sonofusion82/ds32khz_clock/time_update.c

/* 
 * File:   time_update.c
 * Author: YewMing, Chen (fusion82@gmail.com)
 *
 * Created on November 15, 2015, 12:07 AM
 */

#include "time_update.h"

extern volatile unsigned char tmr1_ticked;
extern unsigned char display_ticked;
extern unsigned char low_power_enable;
unsigned char hours = 0;
unsigned char minutes = 0;
unsigned char seconds = 0;
unsigned int temp = 0;

/* unsigned char to 2 byte BCD
 * 
 * NOTE: it assumes n is less than 100
 */
static void toBcd(unsigned char n, unsigned char* bcd)
{
    unsigned char x = 0;
    while (n >= 10)
    {
        n -= 10;
        x++;
    }
    bcd[0] = x;
    bcd[1] = n;
}

void incrementMinute()
{
    minutes++;
    if (minutes >= 60)
    {
        minutes = 0;
        incrementHour();
    }
}

void incrementHour()
{
    hours++;
    if (hours >= 24)
    {
        hours = 0;
    }
}

    
/* Update time
 */
void time_update(unsigned char *bcdTime)
{
    static unsigned char state = 0;
    unsigned char temp_hours;
    
    /* Clock calculation block
     * Uses a state machine to break the operation into smaller chunks to
     * fix display flickering when calculation took too long and it impacts
     * the display refresh periods
     */
    if (display_ticked)
    {
        display_ticked = 0;

        switch (state)
        {
            default:
            case 0:
                if (tmr1_ticked)
                {
                    tmr1_ticked = 0;
                    
                    seconds++;
                    if (seconds >= 60)
                    {
                        seconds = 0;
                        incrementMinute();
                    }

                    state = 1;
                }
                break;
                
            case 1:
                /* low power mode between 12am to 5am */
                /*if (hours < 5)
                {
                    low_power_enable = 1;
                }*/
                /* display in 12 hour format */
                temp_hours = (hours > 12) ? (hours - 12) : hours;
                toBcd(temp_hours, &bcdTime[0]);
                state = 2;
                break;
                
            case 2:
                toBcd(minutes, &bcdTime[2]);
                state = 0;
                break;
        }
    }
}
